USI-Showroom/SmartHouse/Images/arduino_uno.png

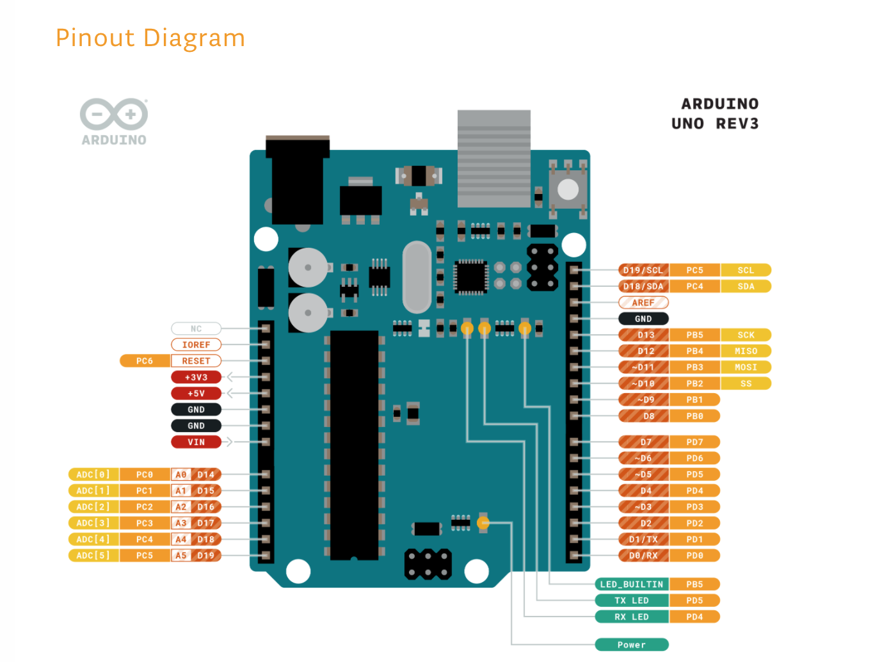
Images/arduino_uno.png
