USI-Showroom/SmartHouse/Images/Due.png

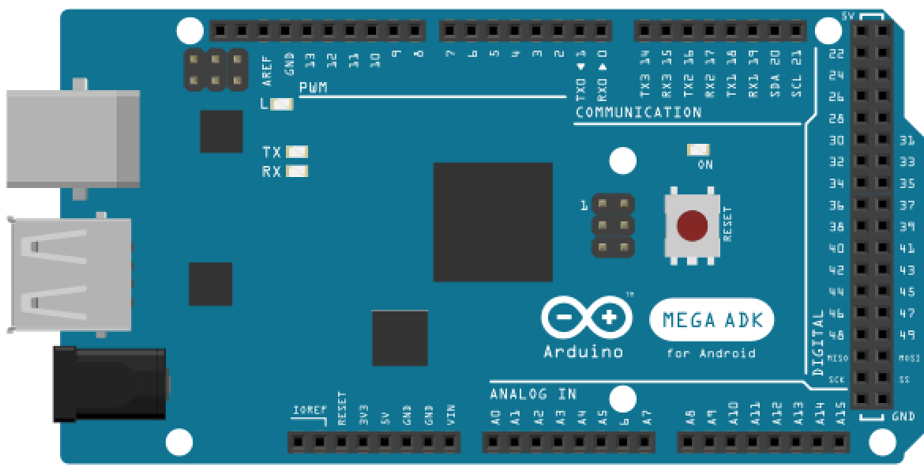
Images/Due.png
