USI-Showroom/SmartHouse/Images/fan.png

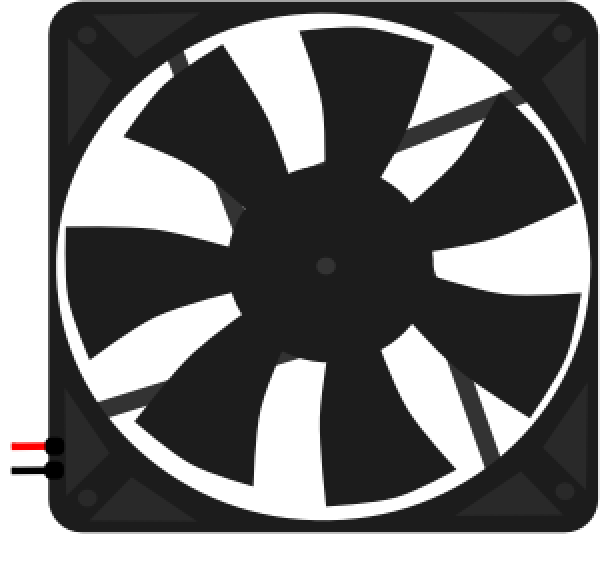
Images/fan.png
