USI-Showroom/SmartHouse/Images/garage.png

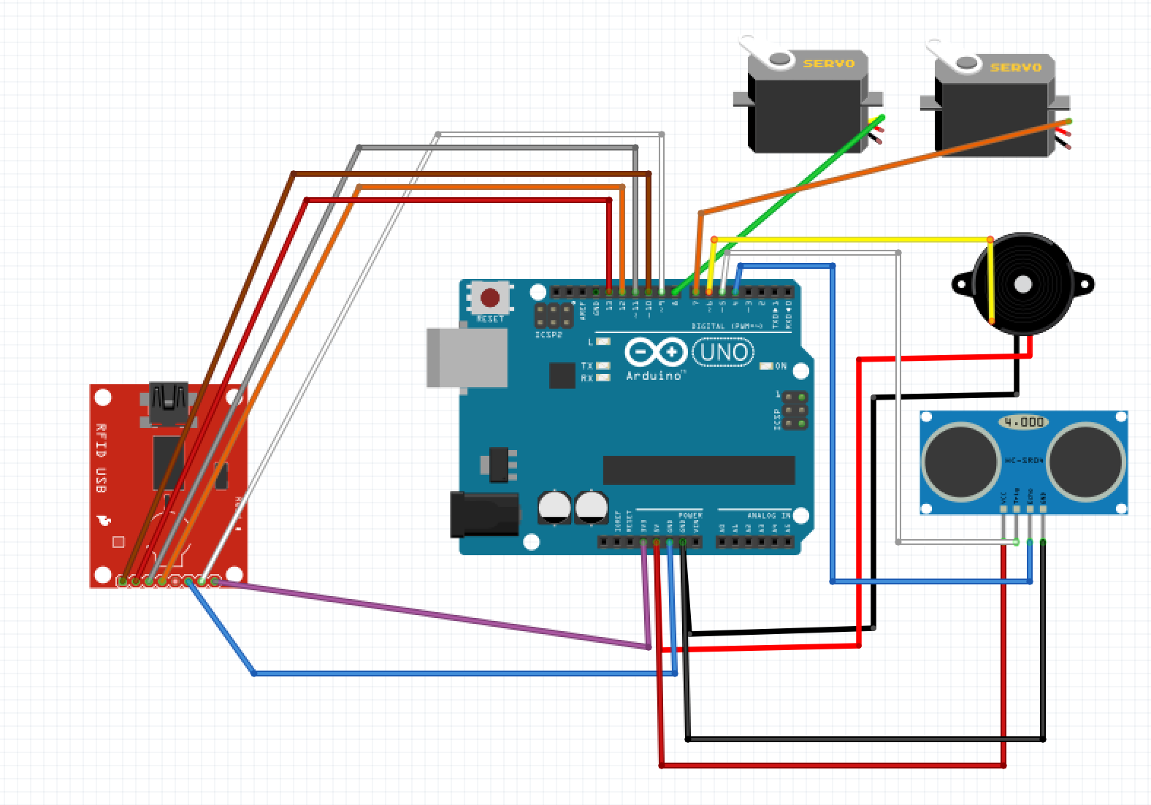
Images/garage.png
