USI-Showroom/SmartHouse/Images/house_map.png

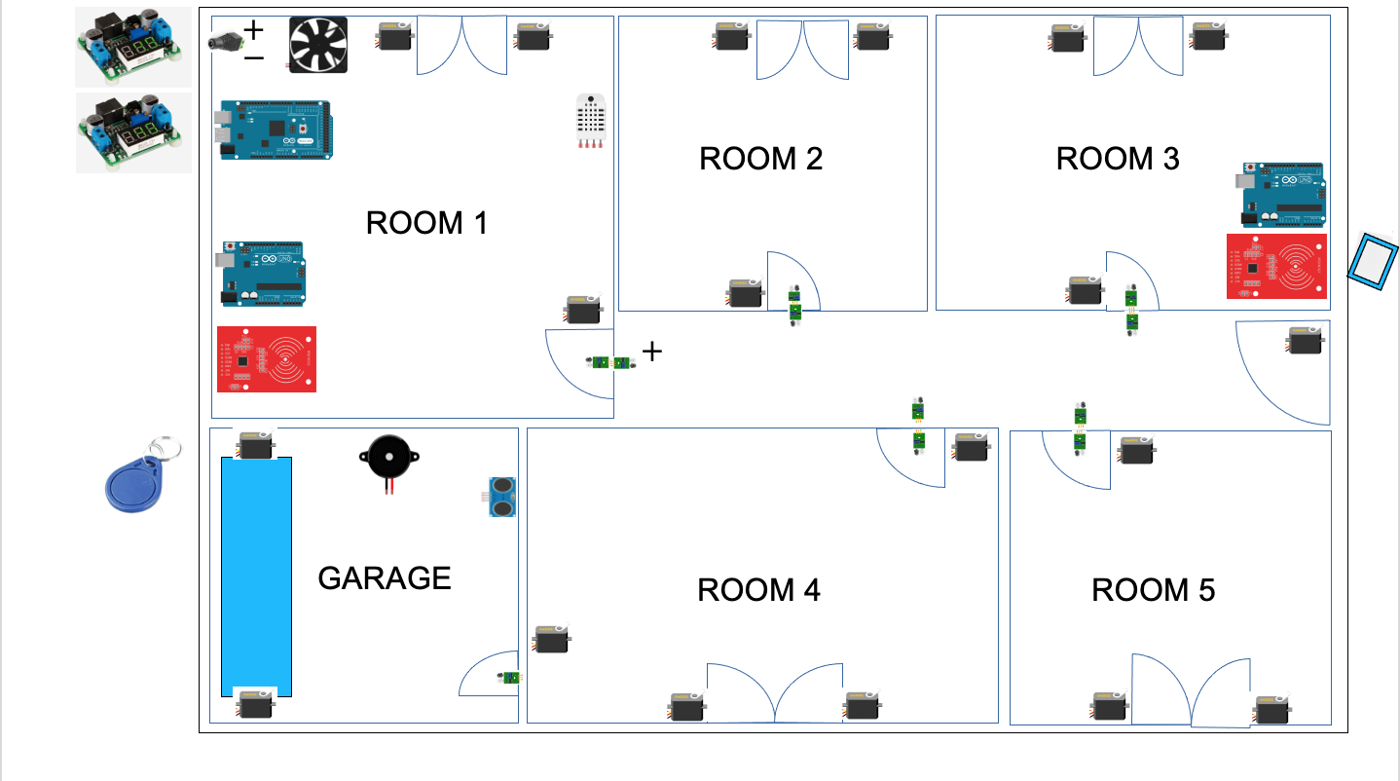
Images/house_map.png
