USI-Showroom/SmartHouse/Images/servo.png

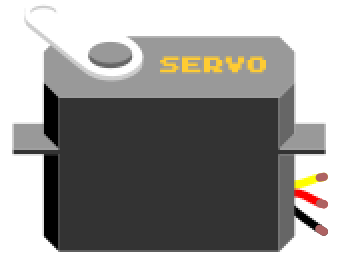
Images/servo.png
