USI-Showroom/SmartHouse/Images/temperature_sensor.png

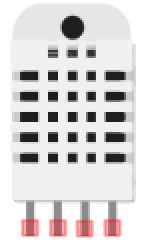
Images/temperature_sensor.png
