USI-Showroom/SmartHouse/Images/Ultrasonic_sensor.png

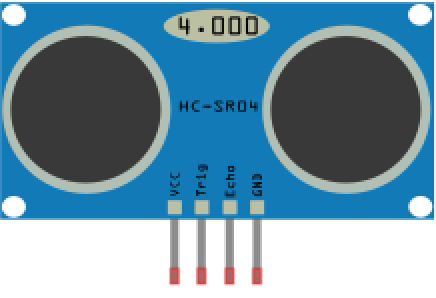
Images/Ultrasonic_sensor.png
